KerCrafter/FPGA-LEDs-Racer/schematic/race_4_players/de0_nano_mini.kicad_sch

## KiCad design schematic/race_4_players/de0_nano_mini.kicad_sch (2025-08-03)

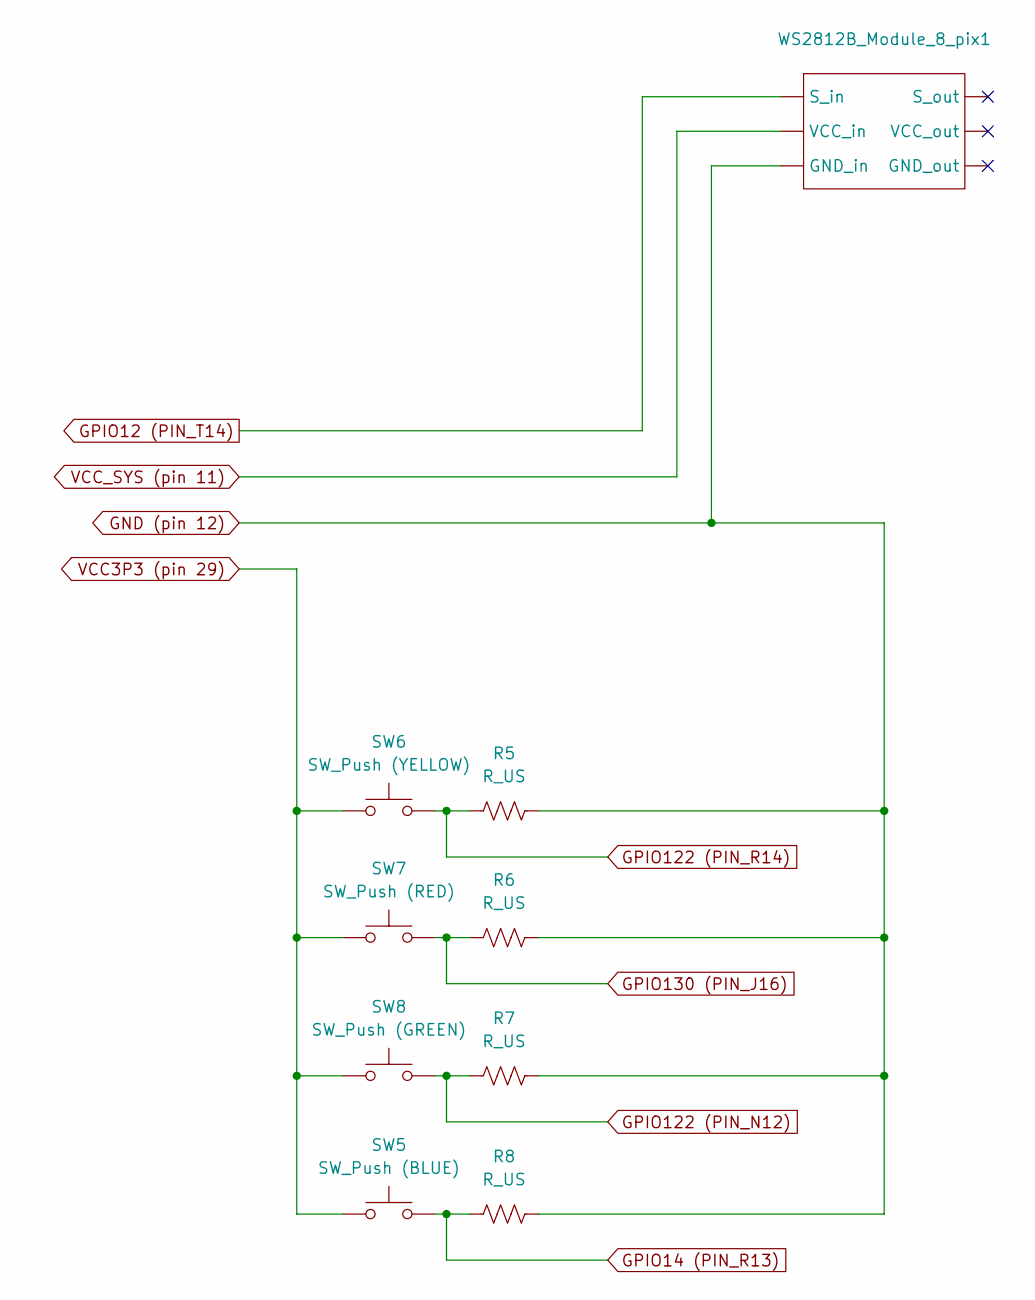
[picture p16: schematic de0_nano_mini.kicad_sch]

Parts:
R5, R6, R7, R8: R_US
SW5: SW_Push (BLUE)
SW6: SW_Push (YELLOW)
SW7: SW_Push (RED)
SW8: SW_Push (GREEN)
WS2812B_Module_8_pix1: (no value)

Connections:
GND (pin 12): R5.2, R6.2, R7.2, R8.2, WS2812B_Module_8_pix1.
GPIO12 (PIN_T14): WS2812B_Module_8_pix1.
GPIO14 (PIN_R13): R8.1, SW5.2
GPIO122 (PIN_N12): R7.1, SW8.2
GPIO122 (PIN_R14): R5.1, SW6.2
GPIO130 (PIN_J16): R6.1, SW7.2
VCC3P3 (pin 29): SW5.1, SW6.1, SW7.1, SW8.1
VCC_SYS (pin 11): WS2812B_Module_8_pix1.
