KerCrafter/FPGA-LEDs-Racer/schematic/race_4_players/race_4_players.kicad_sch

## KiCad design schematic/race_4_players/race_4_players.kicad_sch (2025-08-03)

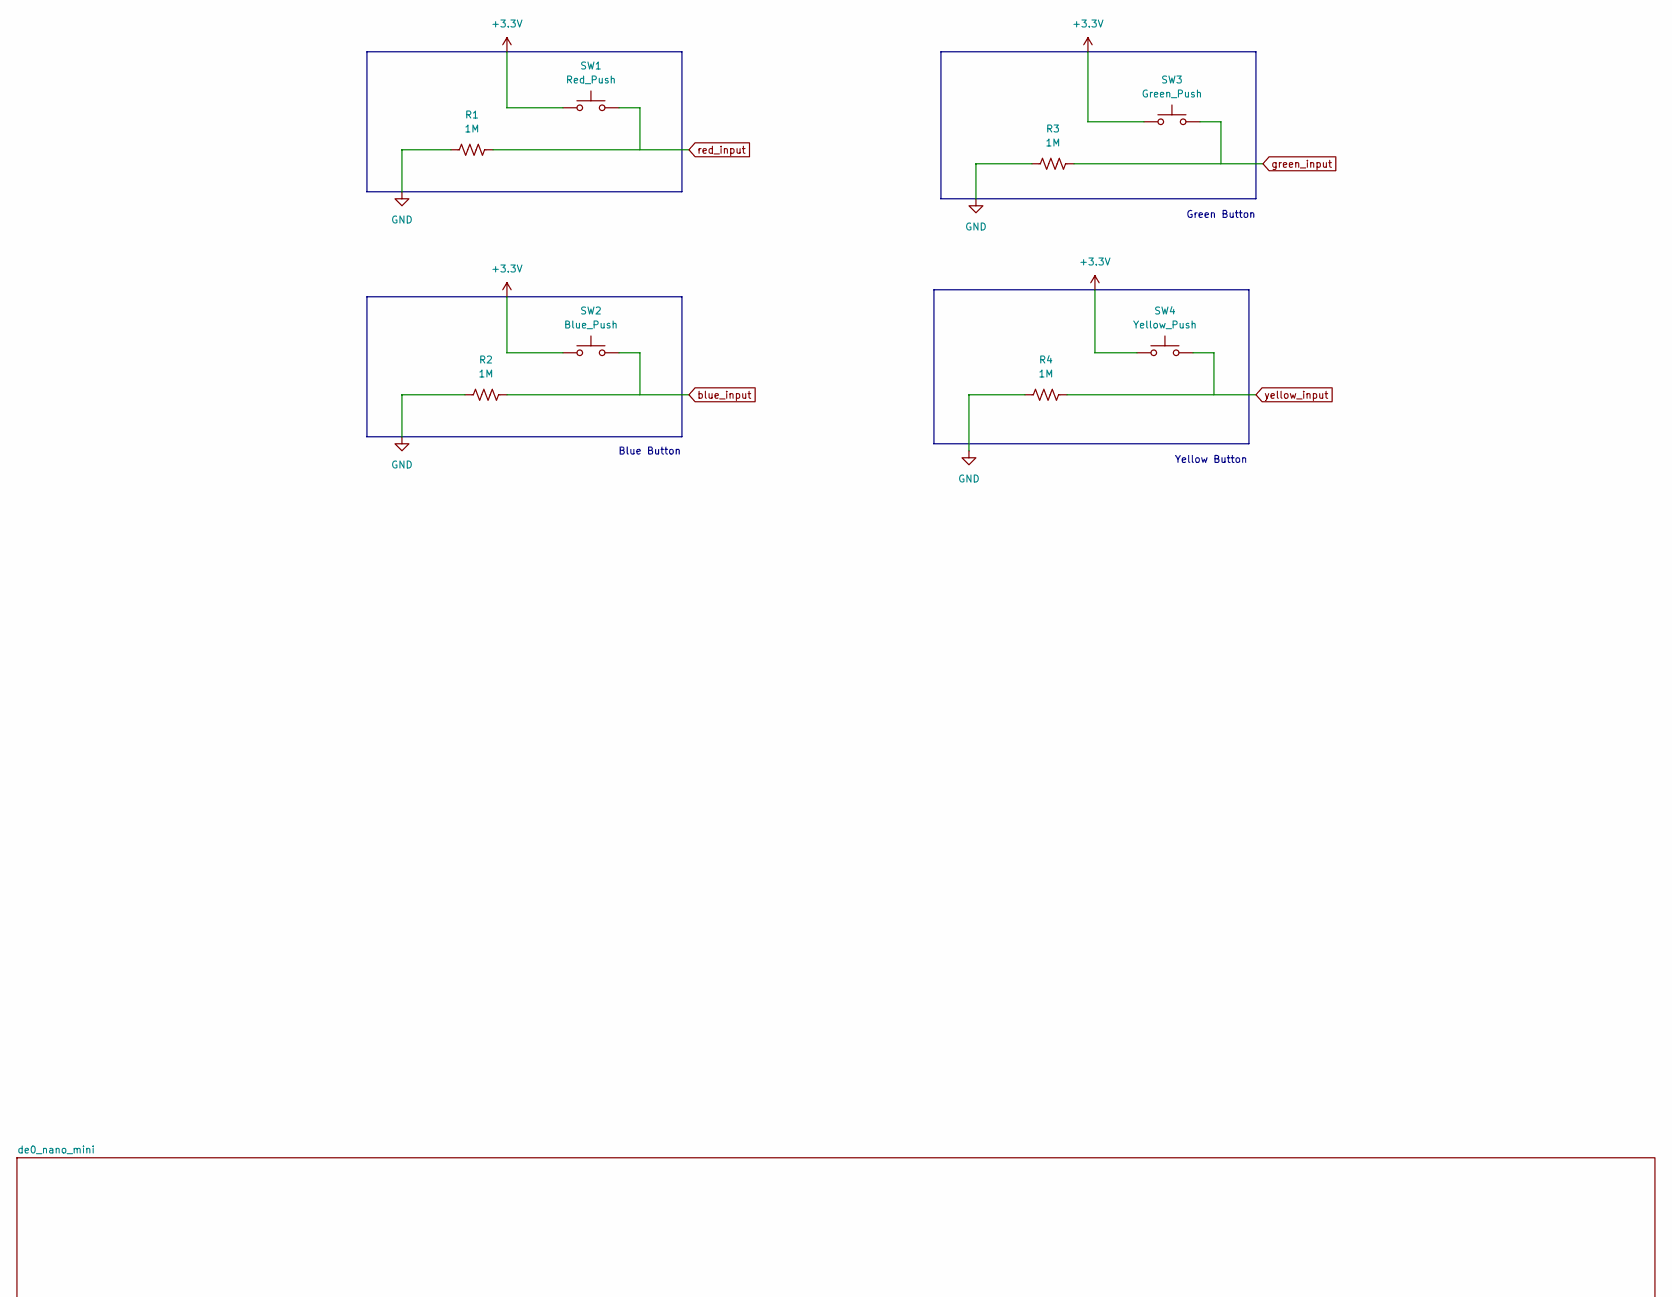
[picture p17: schematic race_4_players.kicad_sch, part in row 1, column 1]

Parts:
R1, R2, R3, R4: 1M
SW1: Red_Push
SW2: Blue_Push
SW3: Green_Push
SW4: Yellow_Push

Connections:
+3.3V: SW1.1, SW2.1, SW3.1, SW4.1
GND: R1.2, R2.2, R3.2, R4.2
blue_input: R2.1
green_input: R3.1
red_input: R1.1
yellow_input: R4.1

Notes on the sheet:
Blue Button
Green Button
Yellow Button
