KerCrafter/FPGA-LEDs-Racer/src/LEDs_racer_core.vhd

library ieee;
use ieee.std_logic_1164.all;
use ieee.numeric_std.all;
use work.players_commands_pkg.all;

entity LEDs_racer_core is
  generic (
    max_pos : integer := 16;
    MENU_TIMER_CLK_COUNT : integer := 50000000; -- with 50Mhz = 1 second
    END_TIMER_CLK_COUNT : integer := 750000000 -- with 50Mhz = 15 seconds
  );

  port(
    clk : in std_logic;

    players_commands : in t_PLAYERS_COMMANDS;
    
    current_led : in integer range 0 to max_pos-1;
    led_green_intensity : out std_logic_vector(7 downto 0);
    led_red_intensity : out std_logic_vector(7 downto 0);
    led_blue_intensity : out std_logic_vector(7 downto 0);
    update_frame : out std_logic
  );
end entity;

architecture structural of LEDs_racer_core is
  signal red_ready_to_play : std_logic;
  signal red_cur_pos : integer range 0 to max_pos-1;
  signal blue_ready_to_play : std_logic;
  signal blue_cur_pos : integer range 0 to max_pos-1;
  signal green_ready_to_play : std_logic;
  signal green_cur_pos : integer range 0 to max_pos-1;
  signal yellow_ready_to_play : std_logic;
  signal yellow_cur_pos : integer range 0 to max_pos-1;
  
  signal red_activity : std_logic;
  signal blue_activity : std_logic;
  signal green_activity : std_logic;
  signal yellow_activity : std_logic;
  signal menu_activity : std_logic;

  signal current_screen : std_logic_vector(1 downto 0);
  signal is_in_menu : std_logic;
  signal countdown : integer range 0 to 7;

  signal reset_all : std_logic;
begin
  domain_unit: entity work.domain_unit
    generic map(
      max_pos => max_pos,
      MENU_TIMER_CLK_COUNT => MENU_TIMER_CLK_COUNT,
      END_TIMER_CLK_COUNT => END_TIMER_CLK_COUNT 
    )
    port map (
      clk => clk,

      players_commands => players_commands,

      current_screen => current_screen,

      red_ready_to_play => red_ready_to_play,
      red_cur_pos => red_cur_pos,
      blue_ready_to_play => blue_ready_to_play,
      blue_cur_pos => blue_cur_pos,
      green_ready_to_play => green_ready_to_play,
      green_cur_pos => green_cur_pos,
      yellow_ready_to_play => yellow_ready_to_play,
      yellow_cur_pos => yellow_cur_pos,
    
      red_activity => red_activity,
      blue_activity => blue_activity,
      green_activity => green_activity,
      yellow_activity => yellow_activity,
      menu_activity => menu_activity,

      is_in_menu => is_in_menu,
      countdown => countdown,
      reset_all => reset_all
    );
  display_unit : entity work.display_unit
    generic map(
      max_pos => max_pos
    )
    port map (
      clk => clk,

      current_led => current_led,

      current_screen => current_screen,

      red_ready_to_play => red_ready_to_play,
      red_cur_pos => red_cur_pos,
      blue_ready_to_play => blue_ready_to_play,
      blue_cur_pos => blue_cur_pos,
      green_ready_to_play => green_ready_to_play,
      green_cur_pos => green_cur_pos,
      yellow_ready_to_play => yellow_ready_to_play,
      yellow_cur_pos => yellow_cur_pos,
    
      red_activity => red_activity,
      blue_activity => blue_activity,
      green_activity => green_activity,
      yellow_activity => yellow_activity,
      menu_activity => menu_activity,

      is_in_menu => is_in_menu,
      countdown => countdown,
      reset_all => reset_all,

      led_green_intensity => led_green_intensity,
      led_red_intensity => led_red_intensity,
      led_blue_intensity => led_blue_intensity,
      update_frame => update_frame
    );

end architecture;
