KerCrafter/FPGA-LEDs-Racer/src/screen_manager/screens/gameplay_screen.vhd

library ieee;
use ieee.std_logic_1164.all;
use ieee.numeric_std.all;

entity gameplay_screen is
  generic (
    max_pos : integer := 109
  );

  port (
    enable : in std_logic;

    red_pos : in integer range 0 to max_pos-1;
    blue_pos : in integer range 0 to max_pos-1;
    green_pos : in integer range 0 to max_pos-1;
    yellow_pos : in integer range 0 to max_pos-1;
    
    led_number : in integer range 0 to max_pos-1;

    i_red_intensity : in std_logic_vector(7 downto 0);
    i_blue_intensity : in std_logic_vector(7 downto 0);
    i_green_intensity : in std_logic_vector(7 downto 0);
  
    o_red_intensity : out std_logic_vector(7 downto 0);
    o_blue_intensity : out std_logic_vector(7 downto 0);
    o_green_intensity : out std_logic_vector(7 downto 0)
  );
end entity;


architecture beh of gameplay_screen is
  signal red_intensity : std_logic_vector(7 downto 0);
  signal blue_intensity : std_logic_vector(7 downto 0);
  signal green_intensity : std_logic_vector(7 downto 0);

  function bool_to_logic(b: boolean) return std_logic is
  begin
     if (b) then
        return '1';
     else
        return '0';
     end if;
  end function bool_to_logic;
begin

  pipe_tri_bus: entity work.pipe_tri_bus
    port map(
      enable => enable,

      i_led_red_intensity => i_red_intensity,
      i_led_blue_intensity => i_blue_intensity,
      i_led_green_intensity => i_green_intensity,

      d_led_green_intensity => green_intensity,
      d_led_red_intensity => red_intensity,
      d_led_blue_intensity => blue_intensity,

      o_led_green_intensity => o_green_intensity,
      o_led_red_intensity => o_red_intensity,
      o_led_blue_intensity => o_blue_intensity
    );

  process(led_number, red_pos, blue_pos, green_pos, yellow_pos)
    variable players_into_the_led : std_logic_vector(3 downto 0);
    
    procedure set_GRB (green_intensity_i: integer range 0 to 255; red_intensity_i: integer range 0 to 255; blue_intensity_i: integer range 0 to 255) is
    begin
      green_intensity <= std_logic_vector(to_unsigned(green_intensity_i, 8));
      red_intensity <= std_logic_vector(to_unsigned(red_intensity_i, 8));
      blue_intensity <= std_logic_vector(to_unsigned(blue_intensity_i, 8));
    end procedure;
    
    procedure set_LED_white is
    begin
      set_GRB(5, 5, 5);
    end procedure;
    
    procedure set_LED_off is
    begin
      set_GRB(0, 0, 0);
    end procedure;
    
    procedure set_LED_green is
    begin
      set_GRB(10, 0, 0);
    end procedure;

    procedure set_LED_red is
    begin
      set_GRB(0, 10, 0);
    end procedure;
    
    procedure set_LED_blue is
    begin
      set_GRB(0, 0, 10);
    end procedure;

    procedure set_LED_yellow is
    begin
      set_GRB(5, 5, 0);
    end procedure;
  begin
    players_into_the_led := bool_to_logic(green_pos = led_number) & bool_to_logic(red_pos = led_number) & bool_to_logic(blue_pos = led_number) & bool_to_logic(yellow_pos = led_number);

    case players_into_the_led is
      when "0000" =>
        set_LED_off;
        
      when "1000" =>
        set_LED_green;
        
      when "0100" =>
        set_LED_red;
        
      when "0010" =>
        set_LED_blue;
        
      when "0001" =>
        set_LED_yellow;

      when others =>
        set_LED_white;
    end case;

  end process;

end architecture;
