KerCrafter/FPGA-LEDs-Racer/src/LEDs_racer_core_blue_wins_tb.vhd

library ieee;
use ieee.std_logic_1164.all;
use ieee.numeric_std.all;

entity LEDs_racer_core_blue_wins_tb is
  port (
    tb_end : out std_logic := '0'
  );
end entity;

architecture simulation of LEDs_racer_core_blue_wins_tb is
  signal clk : std_logic := '0';

  signal red_input : std_logic := '0';
  signal blue_input : std_logic := '0';
  signal green_input : std_logic := '0';
  signal yellow_input : std_logic := '0';
  
  signal current_led : integer range 0 to 4;
  signal led_green_intensity : std_logic_vector(7 downto 0);
  signal led_red_intensity : std_logic_vector(7 downto 0);
  signal led_blue_intensity : std_logic_vector(7 downto 0);
  
  signal update_frame : std_logic;
begin
  UUT: entity work.LEDs_racer_core
    generic map(max_pos => 5)
    port map (
      clk => clk,

      green_input => green_input,
      red_input => red_input,
      blue_input => blue_input,
      yellow_input => yellow_input,
      
      current_led => current_led,
      led_green_intensity => led_green_intensity,
      led_red_intensity => led_red_intensity,
      led_blue_intensity => led_blue_intensity,
      update_frame => update_frame
    );
  
  PLAYS_STIM: process
    procedure assert_GRB(
      led_green_intensity_i: integer range 0 to 255;
      led_red_intensity_i: integer range 0 to 255;
      led_blue_intensity_i: integer range 0 to 255;
      report_message: string
    ) is
    begin
      assert led_green_intensity = std_logic_vector(to_unsigned(led_green_intensity_i, 8)) and led_red_intensity = std_logic_vector(to_unsigned(led_red_intensity_i, 8)) and led_blue_intensity = std_logic_vector(to_unsigned(led_blue_intensity_i, 8)) report report_message severity failure;
    end procedure;
    
    procedure BLUE_player_press_his_button_during(duration: time) is
    begin
      wait for 20 ns;

      blue_input <= '1';
      wait for duration;
      blue_input <= '0';
    end procedure;
    
    procedure assert_all_LEDs_should_be_BLUE is
    begin
      wait for 20 ns; current_led <= 0; wait for 1 ps; assert_GRB(0, 0, 10, "LED 0 : should be BLUE");
      wait for 20 ns; current_led <= 1; wait for 1 ps; assert_GRB(0, 0, 10, "LED 1 : should be BLUE");
      wait for 20 ns; current_led <= 2; wait for 1 ps; assert_GRB(0, 0, 10, "LED 2 : should be BLUE");
      wait for 20 ns; current_led <= 3; wait for 1 ps; assert_GRB(0, 0, 10, "LED 3 : should be BLUE");
      wait for 20 ns; current_led <= 4; wait for 1 ps; assert_GRB(0, 0, 10, "LED 4 : should be BLUE");
    end procedure;
  begin   
    BLUE_player_press_his_button_during(20 ns); --BLUE Player, UP from position 0 to 1
    BLUE_player_press_his_button_during(20 ns); --BLUE Player, UP from position 1 to 2
    BLUE_player_press_his_button_during(20 ns); --BLUE Player, UP from position 2 to 3
    BLUE_player_press_his_button_during(20 ns); --BLUE Player, UP from position 3 to 4
    
    assert_all_LEDs_should_be_BLUE;
    
    -- Game is END Should lock BLUE actions
    BLUE_player_press_his_button_during(20 ns); --BLUE player STAY in position 4

    assert_all_LEDs_should_be_BLUE;

    tb_end <= '1'; wait;

  end process;
  
  CLK_STIM: process
  begin
    -- Inverse CLK every 10ns = 20ns per cycle = 50MHz
    clk <= not clk; wait for 10 ns;
  end process;

end architecture;
