KerCrafter/FPGA-LEDs-Racer/src/simulations/LEDs_racer_core_menu_green_ready_to_play_sim.vhd

library ieee;
use ieee.std_logic_1164.all;
use ieee.numeric_std.all;
use work.test_status_pkg.all;
use work.players_commands_pkg.all;
use work.player_interactions_test_pkg.all;
use work.sut_pkg.all;
use work.assertions_pkg.all;

entity LEDs_racer_core_menu_green_ready_to_play_sim is
  port (
    test_status : out t_TEST_STATUS := TEST_STATUS_INIT
  );
end entity;

architecture simulation of LEDs_racer_core_menu_green_ready_to_play_sim is
  signal SUT : LEDs_racer_core_sut_interface := SUT_INIT;
begin
  UUT: entity work.LEDs_racer_core_SUT
    port map (
      sut_interface => SUT
    );
  
  SIMULATION: process
  begin
    player_press_his_button_during(20 ns, SUT.clk, SUT.players_commands.green);

    assert_LED_should_lightoff(SUT, SUT.current_led, test_status, 7);

    assert_LED_should_be_green_for_range(
      from_led => 8,
      to_led => 13,
      sut => SUT,
      current_led_sig => SUT.current_led,
      test_status => test_status
    );

    assert_LED_should_be_green_for_range(
      from_led => 35,
      to_led => 39,
      sut => SUT,
      current_led_sig => SUT.current_led,
      test_status => test_status
    );

    assert_LED_should_be_green_for_range(
      from_led => 58,
      to_led => 61,
      sut => SUT,
      current_led_sig => SUT.current_led,
      test_status => test_status
    );

    assert_LED_should_be_green_for_range(
      from_led => 77,
      to_led => 79,
      sut => SUT,
      current_led_sig => SUT.current_led,
      test_status => test_status
    );

    assert_LED_should_be_green_for_range(
      from_led => 92,
      to_led => 93,
      sut => SUT,
      current_led_sig => SUT.current_led,
      test_status => test_status
    );

    assert_LED_should_be_green(SUT, SUT.current_led, test_status, 103);

    assert_LED_should_lightoff(SUT, SUT.current_led, test_status, 14);

    SIMULATION_END(test_status);
  end process;

end architecture;
